MgwenaHulela/EEE4113-Monitoring-African-Penguin-During-Molting/Electronics and Controls Subsystem/1_sys_data/images/20250525_024816_FAE53502.jpeg

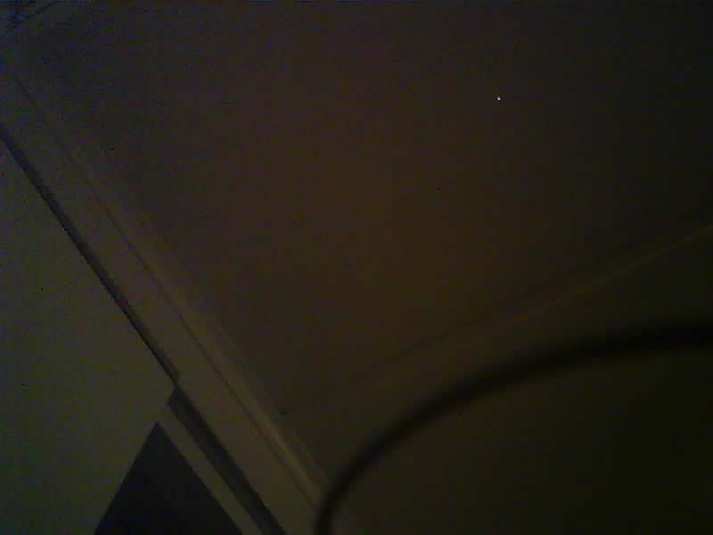
Electronics and Controls Subsystem/1_sys_data/images/20250525_024816_FAE53502.jpeg
