MgwenaHulela/EEE4113-Monitoring-African-Penguin-During-Molting/Electronics and Controls Subsystem/1_sys_data/images/20250525_024830_2A0D4602.jpeg

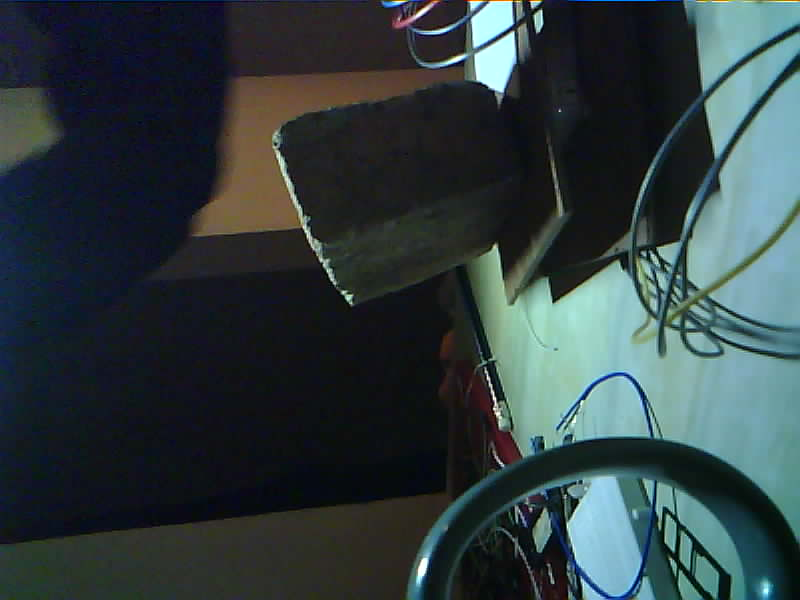
Electronics and Controls Subsystem/1_sys_data/images/20250525_024830_2A0D4602.jpeg
