MgwenaHulela/EEE4113-Monitoring-African-Penguin-During-Molting/Electronics and Controls Subsystem/1_sys_data/images/20250525_025257_7743C001.jpeg

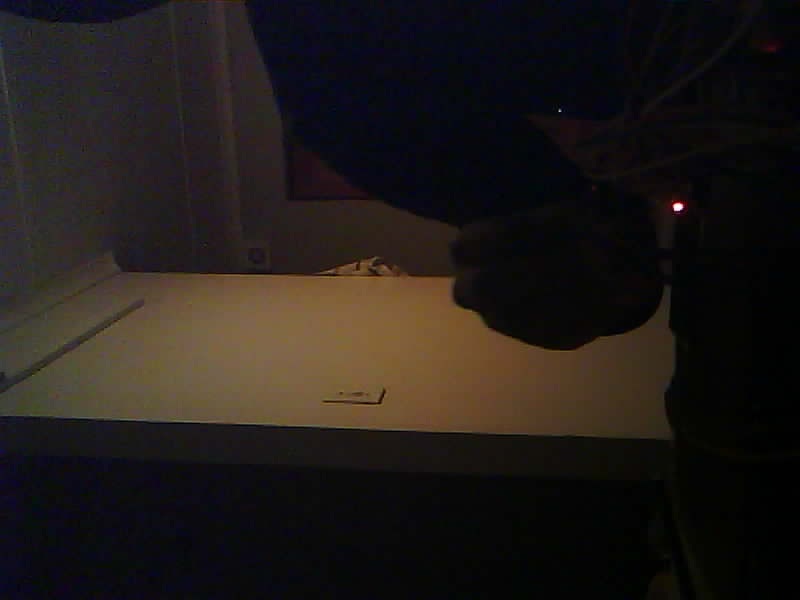
Electronics and Controls Subsystem/1_sys_data/images/20250525_025257_7743C001.jpeg
