MgwenaHulela/EEE4113-Monitoring-African-Penguin-During-Molting/molting_detection_and_ui/models/summary report/loss_curve_fold0.png

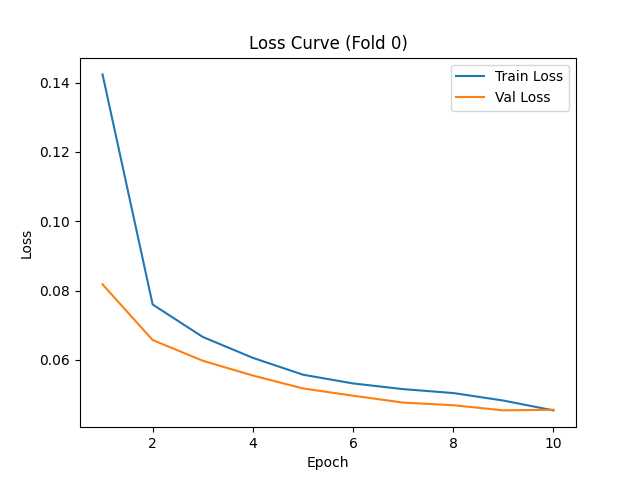
molting_detection_and_ui/models/summary report/loss_curve_fold0.png
