MgwenaHulela/EEE4113-Monitoring-African-Penguin-During-Molting/Electronics and Controls Subsystem/Report_Testing/Temperatur_Humidity_Validation/temperature_plot.png

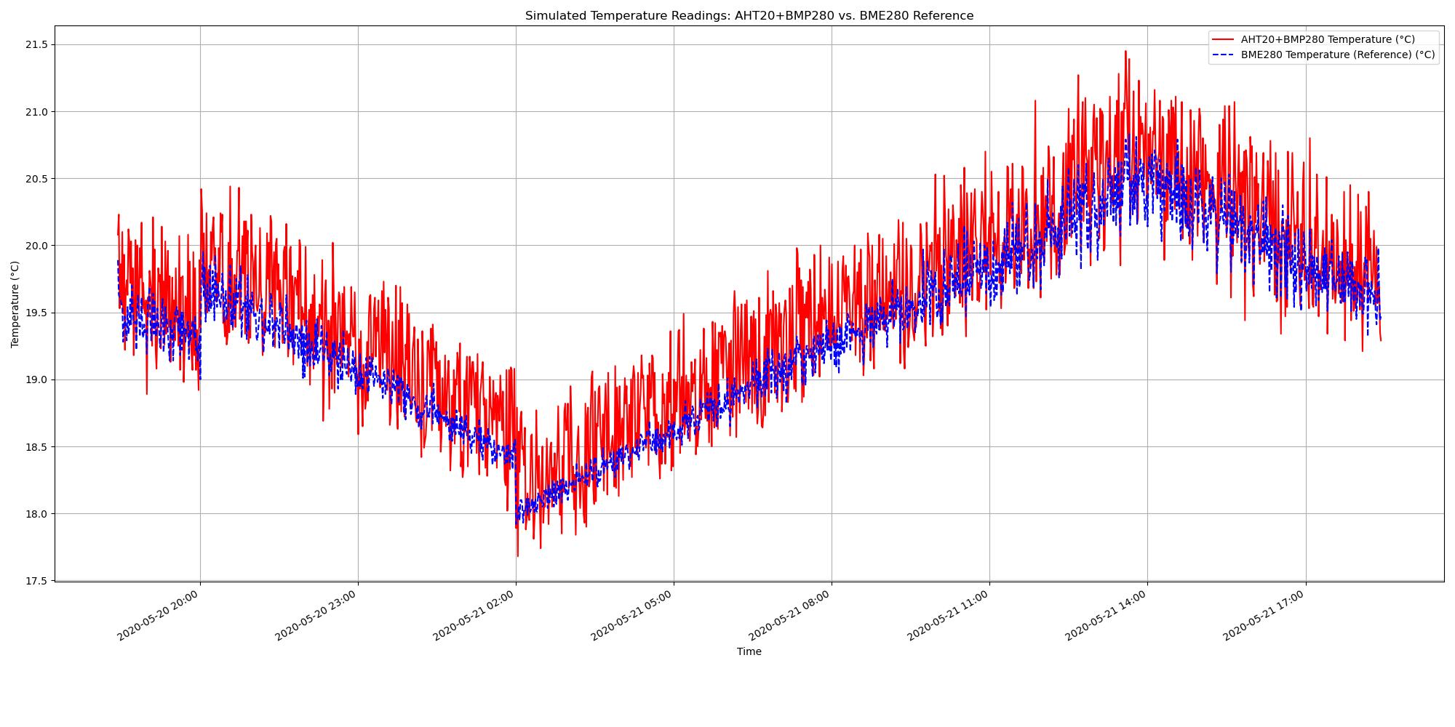
Electronics and Controls Subsystem/Report_Testing/Temperatur_Humidity_Validation/temperature_plot.png
